rhit-staustc/iot-pet-tracker/Production/Booster/Booster.ino

/* Heltec Automation Ping Pong communication test example
 *
 * Function:
 * 1. Ping Pong communication in two esp32 device.
 * 
 * Description:
 * 1. Only hardware layer communicate, no LoRaWAN protocol support;
 * 2. Download the same code into two esp32 devices, then they will begin Ping Pong test each other;
 * 3. This example is for esp32 hardware basic test.
 *
 * HelTec AutoMation, Chengdu, China
 * 成都惠利特自动化科技有限公司
 * www.heltec.org
 *
 * this project also realess in GitHub:
 * https://github.com/Heltec-Aaron-Lee/WiFi_Kit_series
 * */

#include "LoRaWan_APP.h"
#include "Arduino.h"



#define RF_FREQUENCY                                915000000 // Hz

#define TX_OUTPUT_POWER                             22        // dBm

#define LORA_BANDWIDTH                              0         // [0: 125 kHz,
                                                              //  1: 250 kHz,
                                                              //  2: 500 kHz,
                                                              //  3: Reserved]
#define LORA_SPREADING_FACTOR                       10         // [SF7..SF12]
#define LORA_CODINGRATE                             1         // [1: 4/5,
                                                              //  2: 4/6,
                                                              //  3: 4/7,
                                                              //  4: 4/8]
#define LORA_PREAMBLE_LENGTH                        8         // Same for Tx and Rx
#define LORA_SYMBOL_TIMEOUT                         0         // Symbols
#define LORA_FIX_LENGTH_PAYLOAD_ON                  false
#define LORA_IQ_INVERSION_ON                        false


#define RX_TIMEOUT_VALUE                            1000
#define BUFFER_SIZE                                 30 // Define the payload size here

char txpacket[BUFFER_SIZE];
char rxpacket[BUFFER_SIZE];

static RadioEvents_t RadioEvents;
void OnTxDone( void );
void OnTxTimeout( void );
void OnRxDone( uint8_t *payload, uint16_t size, int16_t rssi, int8_t snr );

struct GPSPacket {
  uint8_t status;  // [reserved(4)|fresh(1)|fix_valid(1)|ID(2)]
  uint8_t battery; // 0-100%
  float lat;
  float lon;
  uint16_t speed;  // mph * 100
  uint16_t course; // degrees * 100
};

typedef enum
{
    LOWPOWER,
    STATE_RX,
    STATE_TX
}States_t;

int16_t txNumber;
States_t state;
bool sleepMode = false;
int16_t Rssi, rxSize;


void setup() {
    Serial.begin(115200);
    Mcu.begin(HELTEC_BOARD,SLOW_CLK_TPYE);
    txNumber = 0;
    Rssi = 0;
    rxSize = 0;  // init so we don't send garbage before first receive

    RadioEvents.TxDone = OnTxDone;
    RadioEvents.TxTimeout = OnTxTimeout;
    RadioEvents.RxDone = OnRxDone;

    Radio.Init( &RadioEvents );
    Radio.SetChannel( RF_FREQUENCY );
    Radio.SetTxConfig( MODEM_LORA, TX_OUTPUT_POWER, 0, LORA_BANDWIDTH,
                                   LORA_SPREADING_FACTOR, LORA_CODINGRATE,
                                   LORA_PREAMBLE_LENGTH, LORA_FIX_LENGTH_PAYLOAD_ON,
                                   true, 0, 0, LORA_IQ_INVERSION_ON, 3000 );

    Radio.SetRxConfig( MODEM_LORA, LORA_BANDWIDTH, LORA_SPREADING_FACTOR,
                                   LORA_CODINGRATE, 0, LORA_PREAMBLE_LENGTH,
                                   LORA_SYMBOL_TIMEOUT, LORA_FIX_LENGTH_PAYLOAD_ON,
                                   0, true, 0, 0, LORA_IQ_INVERSION_ON, true );
    state = STATE_RX;  // start in RX so we wait for a message before echoing
}



void loop()
{
  switch(state)
  {
    case STATE_TX:
      if (rxSize > 0) {  // only send if we have actually received something
        Serial.printf("\r\nResending %d bytes\r\n", rxSize);
        Radio.Send( (uint8_t *)rxpacket, rxSize );  // echo raw bytes using received length
      } else {
        state = STATE_RX;  // nothing to echo yet, go back to listening
        break;
      }
      state = LOWPOWER;
      break;
    case STATE_RX:
      Serial.println("into RX mode");
      Radio.Rx( 0 );
      state = LOWPOWER;
      break;
    case LOWPOWER:
      Radio.IrqProcess( );
      break;
    default:
      break;
  }
}


void OnTxDone( void )
{
  Serial.print("TX done......");
  state = STATE_RX;  // go back to listening after each echo
}

void OnTxTimeout( void )
{
    Radio.Sleep( );
    Serial.print("TX Timeout......");
    state = STATE_TX;  // retry on timeout
}

void OnRxDone( uint8_t *payload, uint16_t size, int16_t rssi, int8_t snr )
{ 
    rxSize = size;                    // save received byte count
    memcpy(rxpacket, payload, size); // copy raw bytes (not strlen-safe for binary)
    Radio.Sleep();
    Serial.printf("Received %d bytes, RSSI: %d\r\n", size, rssi);
    state = STATE_TX;
}
